arcnode-io/edp-module-assemblies/equipment/CMP-PDU-001/envelope.step

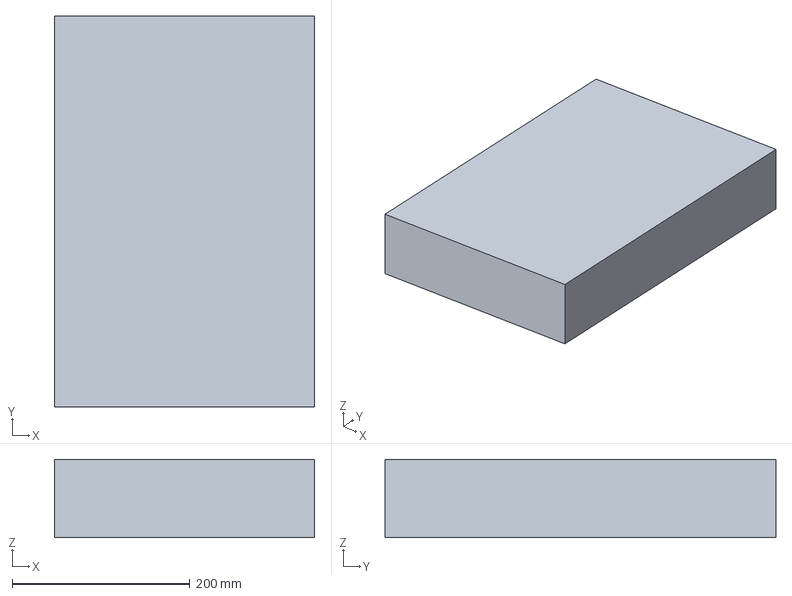
[picture p10: CAD file, 2026-10-03]
equipment/CMP-PDU-001/envelope.step
293.0 x 440.0 x 88.0 mm
