arcnode-io/edp-module-assemblies/equipment/CMP-RACK-001/envelope.step

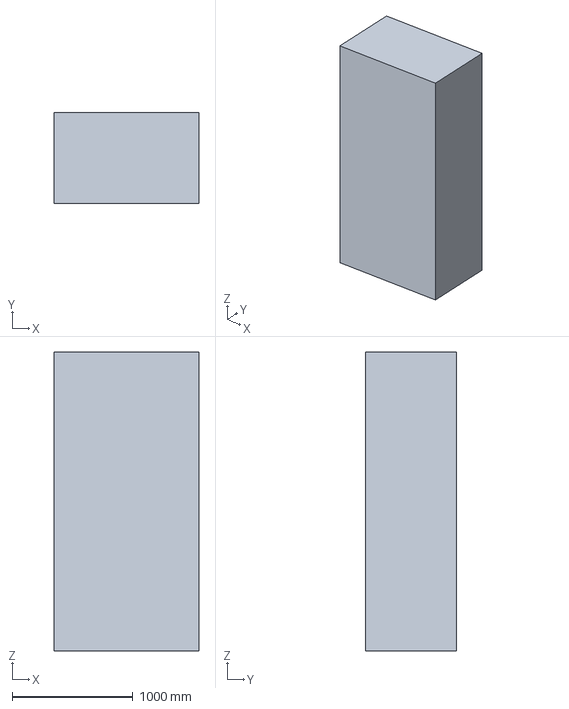
[picture p11: CAD file, 2026-05-09]
equipment/CMP-RACK-001/envelope.step
1200.0 x 750.0 x 2477.0 mm
