arcnode-io/edp-module-assemblies/equipment/CMP-SWITCH-001/envelope.step

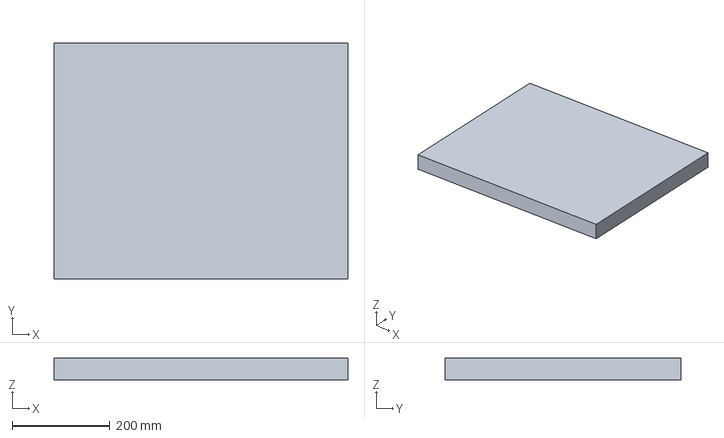
[picture p12: CAD file, 2026-05-09]
equipment/CMP-SWITCH-001/envelope.step
600.0 x 482.0 x 44.0 mm
