arcnode-io/edp-module-assemblies/equipment/CMP-SWITCH-002/envelope.step

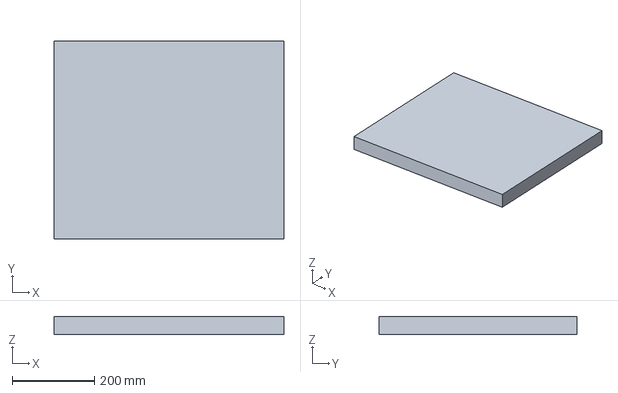
[picture p13: CAD file, 2026-05-09]
equipment/CMP-SWITCH-002/envelope.step
560.0 x 482.0 x 44.0 mm
