arcnode-io/edp-module-assemblies/equipment/EXT-BESS-001/envelope.step

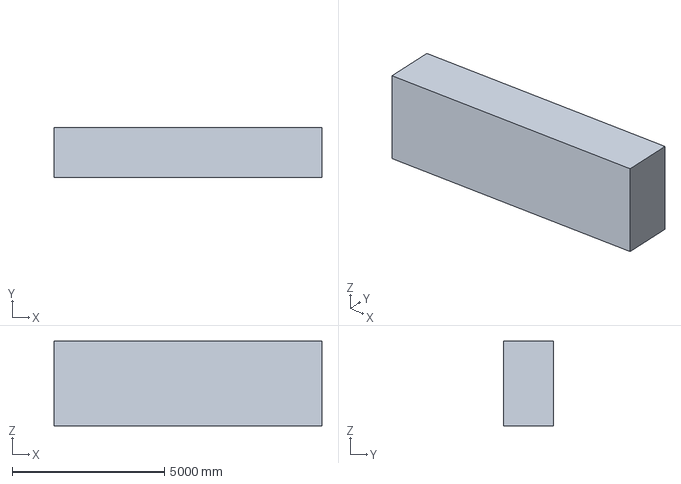
[picture p14: CAD file, 2026-05-09]
equipment/EXT-BESS-001/envelope.step
8800.0 x 1650.0 x 2785.0 mm
