arcnode-io/edp-module-assemblies/equipment/EXT-BESS-002/envelope.step

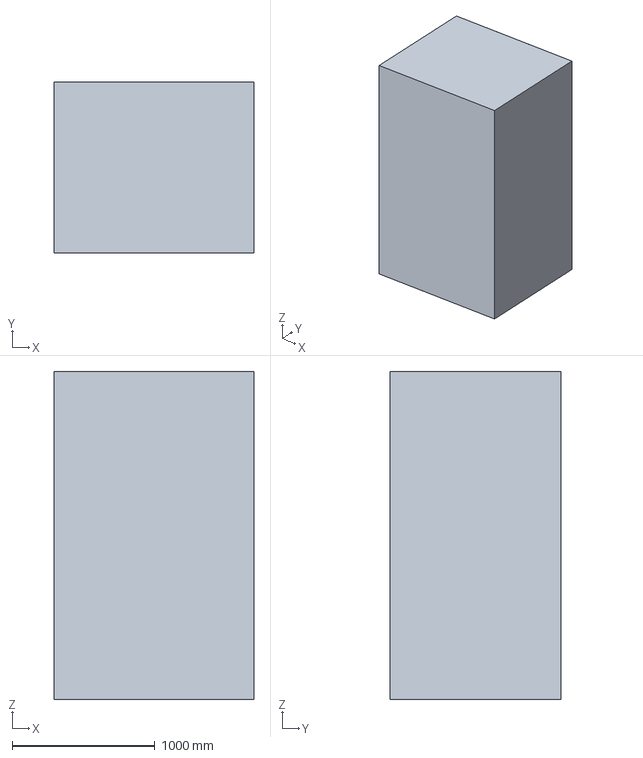
[picture p15: CAD file, 2026-05-09]
equipment/EXT-BESS-002/envelope.step
1400.0 x 1200.0 x 2300.0 mm
