arcnode-io/edp-module-assemblies/equipment/EXT-DC-001/envelope.step

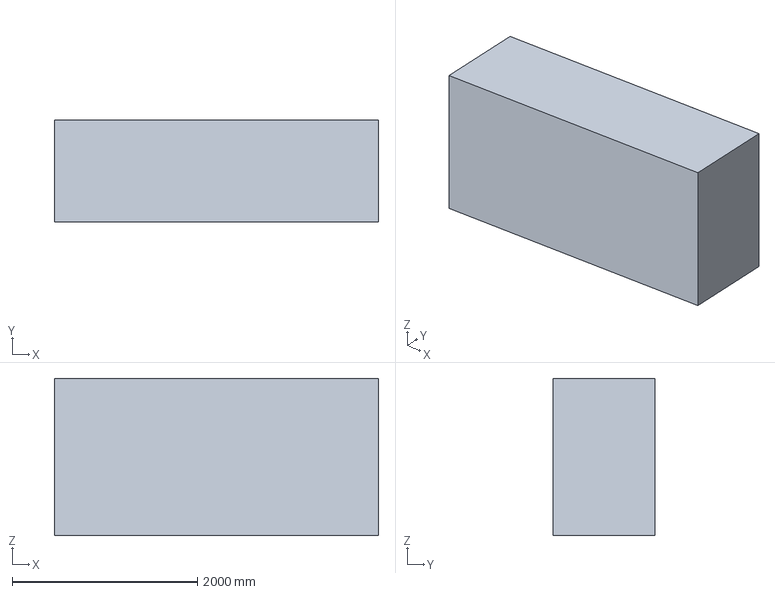
[picture p16: CAD file, 2026-05-09]
equipment/EXT-DC-001/envelope.step
3500.0 x 1100.0 x 1700.0 mm
