arcnode-io/edp-module-assemblies/equipment/EXT-DC-002/envelope.step

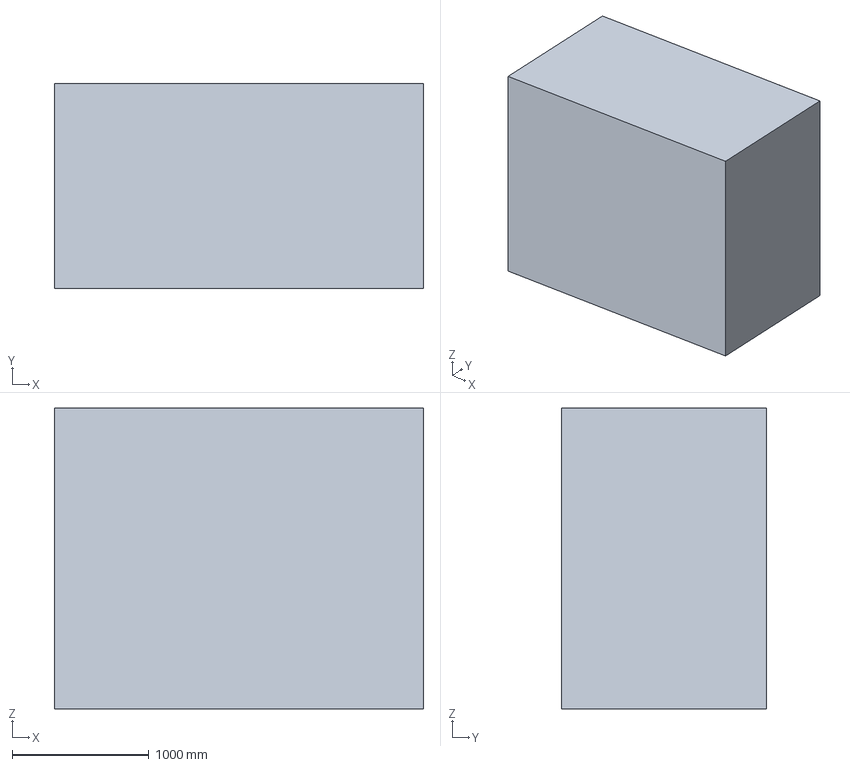
[picture p17: CAD file, 2026-05-09]
equipment/EXT-DC-002/envelope.step
2700.0 x 1500.0 x 2200.0 mm
