arcnode-io/edp-module-assemblies/equipment/GRD-MTR-001/envelope.step

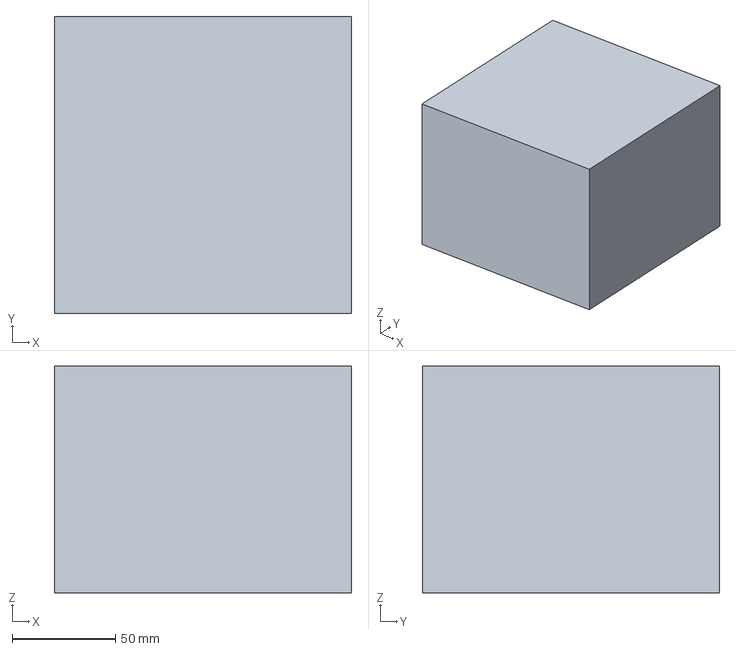
[picture p18: CAD file, 2026-05-09]
equipment/GRD-MTR-001/envelope.step
144.0 x 144.0 x 110.0 mm
