arcnode-io/edp-module-assemblies/equipment/GRD-PCS-001/envelope.step

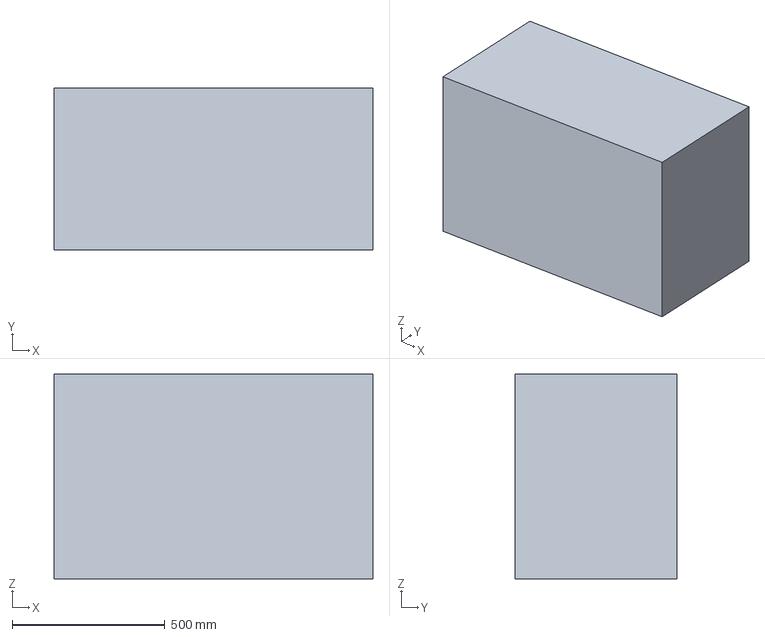
[picture p19: CAD file, 2026-05-09]
equipment/GRD-PCS-001/envelope.step
1045.0 x 530.0 x 670.0 mm
