arcnode-io/edp-module-assemblies/equipment/GRD-RLY-001/envelope.step

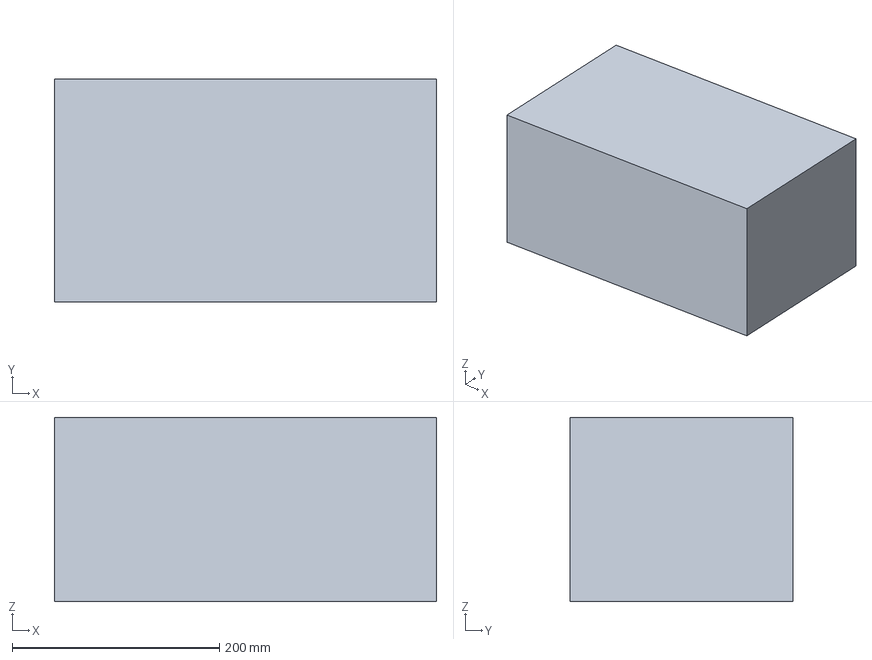
[picture p20: CAD file, 2026-05-09]
equipment/GRD-RLY-001/envelope.step
369.0 x 215.0 x 178.0 mm
