arcnode-io/edp-module-assemblies/equipment/GRD-SWG-001/envelope.step

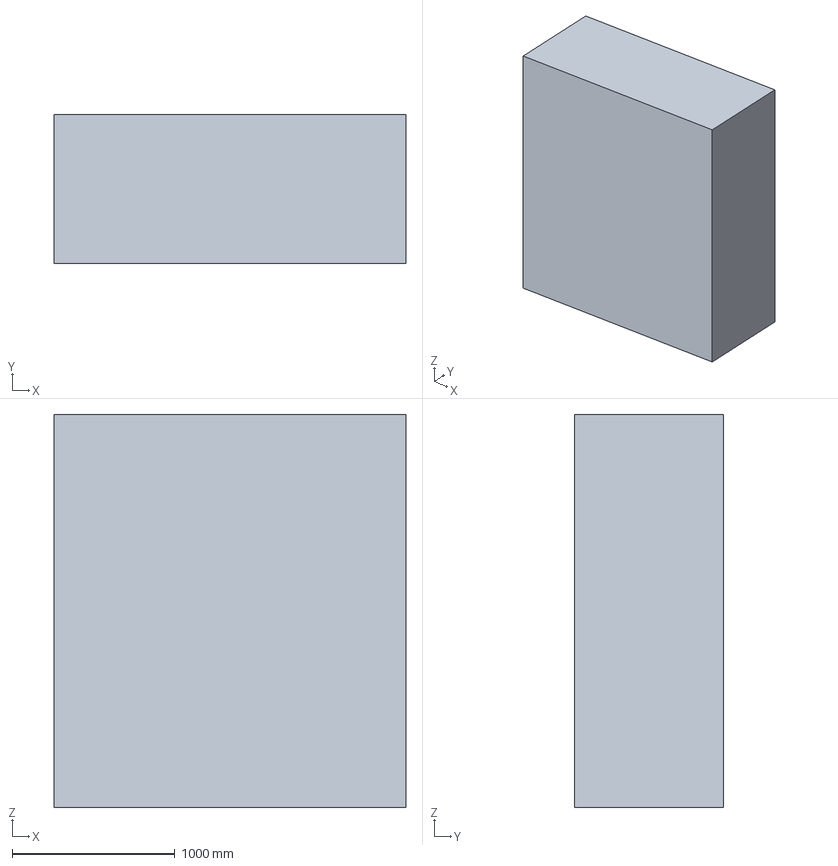
[picture p21: CAD file, 2026-05-09]
equipment/GRD-SWG-001/envelope.step
2159.0 x 914.0 x 2413.0 mm
