arcnode-io/edp-module-assemblies/equipment/GRD-XFM-001/envelope.step

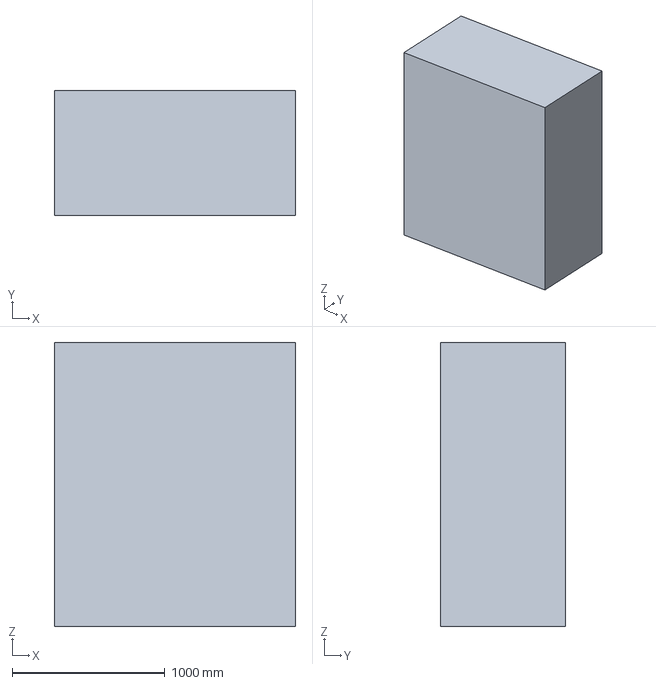
[picture p22: CAD file, 2026-05-09]
equipment/GRD-XFM-001/envelope.step
1580.0 x 820.0 x 1860.0 mm
