arcnode-io/edp-module-assemblies/equipment/CMP-PDU-001/spec.yaml

equipment_id: CMP-PDU-001
schema_version: "1"
category: pdu
vendor: Raritan (Legrand)
model_number: PX4-56A8I2R-C8E8F5V2 (2U horizontal, outlet metered + switched, 415V Wye 60A, 48A rated, 34.5kVA, 18 outlets)
description: 2U horizontal intelligent rack PDU, 415V 3ph Wye 60A (48A rated) 34.5kVA, inlet + branch + outlet metered (Class 0.5) and switched, 18 locking HDOT Cx outlets, Xerus platform
datasheet_url: https://cdn.raritan.com/product-selector/pdus/PX4-56A8I2R-C8E8F5V2/PX4-56A8I2R-C8E8F5V2-spec.pdf
datasheet_hash: TBD_compute_at_pipeline_run
step_source: null
fab_tier: dod_eligible
restricted_entities: null
install_video_url: null  # Track A enrichment — vendor-research pass populates
lead_time_weeks: 4
unit_cost_usd: null

spec:
  electrical:
    voltage_v: 415.0                  # 3-phase line-to-line
    voltage_range_v: [380.0, 440.0]
    current_a: 60.0
    phase: 3ph
    frequency_hz: 60.0
    power_kw: 34.5                    # 34.5 kVA: 415V × 48A rated (60A × 80% continuous) × √3
    power_factor_range: null
    efficiency_pct: null
    breaker_size_a: 60.0
    aic_rating_ka: null
    thd_pct: null
    fault_current_contribution_pu: null

  thermal:
    heat_load_kw: 0.05
    heat_rejection_kw: null
    coolant_compatibility: null
    flow_rate_lpm: null
    supply_temp_c: null
    return_temp_c: null
    pump_head_kpa: null
    internal_pressure_drop_kpa: null
    port_size_dn: null

  mechanical:
    weight_kg: 11.8                   # 26 lb
    dimensions_mm: [293, 440, 88]     # D × W × H
    container_type: 10ft_ISO_high_cube
    mounting: rack_19in
    mounting_notes: |
      2U horizontal in the rack U space (RACK-KIT-PX-2U). The rack's
      zero-U channels take only 4 PDUs, so the 6 needed for 2N go in U
      space. ARCNODE Compute Container uses 6× PDUs in 2N (3× A-side,
      3× B-side): ~13.3 kW each normally; on single-feed failure the
      surviving 3 carry the full ~80 kW at ~26.7 kW each, within the
      34.5 kVA rating. Enabled by 415V LV from GRD-XFM-001 secondary.
    rack_units: 2
    ip_rating: null
    lift_points: null
    ambient_temp_range_c: [-15, 60]
    max_elevation_m: null
    noise_dba_at_1m: null

  ports:
    - port_id: PWR_IN
      type: ac_power
      role: input
      connector_spec: IEC 60309 60A 3P+N+PE 6h pin and sleeve (240/415V Wye, 4P5W)
      mating_part: matching IEC 60309 60A 3P+N+PE 6h socket
      qty: 1
    - port_id: PWR_OUT_HDOT_CX
      type: ac_power
      role: output
      connector_spec: HDOT Cx hybrid C13/C19, locking, 16A (240V phase-to-neutral; 12× 16A branch breakers, 10 kAIC)
      mating_part: C14 or C20 plug
      qty: 18
    - port_id: NET_PRIMARY
      type: ethernet
      role: bidirectional
      connector_spec: RJ45 (Gigabit Ethernet)
      mating_part: null
      qty: 1
    - port_id: NET_SECONDARY
      type: ethernet
      role: bidirectional
      connector_spec: RJ45 (Gigabit Ethernet, redundant network)
      mating_part: null
      qty: 1
    - port_id: USB
      type: usb
      role: bidirectional
      connector_spec: USB-A
      mating_part: null
      qty: 1
    - port_id: SENSOR
      type: signal_digital
      role: input
      connector_spec: RJ45 (Legrand SmartSensor bus)
      mating_part: SmartSensor
      qty: 2

  control:
    protocol: snmp
    register_map_url: https://cdn1.raritan.com/download/pdu-g2/4.1.1/MIB_Usage_4.1.1_49961.pdf  # PDU2-MIB (all Xerus PDUs), inlet + inlet-pole sensor tables
    command_latency_ms: null
    step_response_ms: null
    control_modes:
      - autonomous_local
      - external_setpoint
      - per_outlet_switching
      - last_known_value_fallback
    black_start_capable: null

geometry:
  source: synthesized
  fidelity: bounding_box
  equipment_envelope_path: geometry/envelopes/CMP-PDU-001-equipment.step
  service_envelope_path: geometry/envelopes/CMP-PDU-001-service.step
  bounding_box:
    L_mm: 293.0
    W_mm: 440.0
    H_mm: 88.0
  service_clearance:
    front: 600.0
    rear: 0.0
    left: 50.0
    right: 50.0
    top: 100.0
    bottom: 100.0
    install_clearance: null

provenance:
  authored_by: skill:datasheet_extractor
  authored_date: 2026-04-28
  reviewed_by: TBD_pending_human_review
  reviewed_date: null
  confidence_flags:
    - field: spec.electrical.aic_rating_ka
      flag: missing
    - field: spec.thermal.heat_load_kw
      flag: assumed_default
      note: ~50W typical for intelligent PDU electronics.
    - field: control.command_latency_ms
      flag: missing
    - field: unit_cost_usd
      flag: missing
    - field: lead_time_weeks
      flag: low_confidence_extraction
      note: Server Technology typical 4 weeks for stocked SKUs; longer for custom configurations.

notes: |
  Raritan PX4 2U horizontal is the reference rack PDU for the ARCNODE
  Compute Container. The rack (CMP-RACK-001) has 4 zero-U PDU bays; 2N at
  80 kW on 34.5 kVA PDUs needs 6, so all 6 go in U space as one model.
  PRO3X was dropped (415V tops out at 17.3 kW); PRO4X C4G36RC matches
  electrically but is 0U-only.

  Sizing math for v1 HGX Compute Container (80 kW sustained):
  - 6× PX4 per Compute Container (3× A-side feed, 3× B-side feed)
  - Normal balanced operation: ~13.3 kW per PDU
  - Single-feed failure mode: surviving 3 PDUs carry full 80 kW = 26.7 kW
    each, within 34.5 kVA rating. TRUE 2N redundancy.
  - Headroom for B300/Blackwell Ultra upgrade (10% higher TDP per node):
    surviving-side load at ~88 kW = 29.3 kW per PDU, still within rating.

  HGX B200 power architecture (per CMP-NODE-001):
  - 4× PWS-6K61G-2R 6600W PSUs per node (2+2), each with two C20 inlets
    (16A each) that must both be live; phase-to-neutral 240V on 415Y/240V
  - Per-node sustained: ~10.5 kW; peak PSU capacity: 26.4 kW
  - PDU outlets per node: 8 (PSUs 1-2 → 4 cords on A, PSUs 3-4 → 4 on B);
    never split one PSU's two cords across feeds
  - 7 nodes × 8 = 56 node cords across 6 PDUs (108 Cx outlets), ~9-10 per PDU
  - Plus 2× C13 per ToR switch, 1× C13 per CDU, 1× C13 for ancillary
  - Outlet plan: at most one node cord per 16A branch breaker. A cord runs
    ~5.7A normally and ~11.5A with one feed lost, so two on one breaker
    (~23A) trip it on a feed loss. 12 breakers per PDU cover ~10 cords.
  - Inrush: <30A per PSU inlet (Supermicro), 8 inlets per node; stagger
    power-on across a PDU's breakers.

  HDOT Cx outlets accept either C14 or C20 plugs (16A, same as an IEC
  C19), so HGX node C20 plugs and switch/CDU C14 plugs share one SKU.

  EMS integration: SNMP via PDU2-MIB (Raritan MIB usage guide: applies to
  all Xerus devices, PX2/PX3/PX4 and PRO3X/PRO4X). Also Redfish, Modbus TCP
  and JSON-RPC per the PX4 spec sheet.

  Availability (2026-10-02): listed at PCNation, Tech-America, Connection
  ($3.1k-4.7k), all out of stock; quote Raritan direct.
  Per-outlet on/off control supported, useful for remote node power
  cycling without crash-cart access.

  Cybersecurity: Xerus platform supports HTTPS, SSH, SNMPv3, RADIUS,
  LDAPS, 802.1X, and signed firmware updates. NERC CIP eligible.

  Fab origin: Taiwan (GSA Advantage, GSIN 11000125269132, exact part).
  TAA compliant (Raritan TAA statement; Taiwan is a FAR 25.003 designated
  country); not BAA / Made in USA. Request a certificate of origin from
  Legrand where TAA is contractually load-bearing.

  ADR-005 (415V LV architecture): Trihal secondary set to 415Y/240V
  enables this PDU sizing.
