arcnode-io/edp-module-assemblies/equipment/EXT-BESS-001/spec.yaml

equipment_id: EXT-BESS-001
schema_version: "1"
category: bess
vendor: Tesla
model_number: Megapack 2 XL (PN 1848844-XX-Y)
description: 4 MWh AC-coupled BESS with integrated grid-forming bidirectional inverter
datasheet_url: http://www.cayugacounty.gov/DocumentCenter/View/33252/Tesla-Megapack-Datasheet
datasheet_hash: TBD_compute_at_pipeline_run
step_source: null
fab_tier: federal_civilian
restricted_entities:
  - DOD_1260H
install_video_url: null  # Track A enrichment — vendor-research pass populates
lead_time_weeks: null
unit_cost_usd: null

spec:
  electrical:
    voltage_v: 480.0
    voltage_range_v: null              # single nominal voltage
    current_a: 2887.0                  # computed: 2400 kVA / (480 × √3), 2-hour max
    phase: 3ph
    frequency_hz: 60.0                 # 50/60 Hz configurable
    power_kw: 1927.0                   # 2-hour rated AC power, C010/C011
    power_factor_range: null
    efficiency_pct: 91.7               # round-trip system efficiency, 2-hour C010/C011
    breaker_size_a: null
    aic_rating_ka: null
    thd_pct: null
    fault_current_contribution_pu: null

  thermal: null                         # external BESS handles its own thermal

  mechanical:
    weight_kg: 38100.0
    dimensions_mm: [8800, 1650, 2785]  # L × W × H (W 8800 × D 1650 × H 2785 per datasheet)
    container_type: null
    mounting: pad
    mounting_notes: |
      Pad-mounted with seismic anchoring per local code. Customer-owned pad
      civil works. Service clearance and access are customer site planning,
      not ARCNODE Grid Container integration.
    rack_units: null
    ip_rating: IP66                    # main enclosure; thermal system is IP20
    lift_points: null
    ambient_temp_range_c: [-30, 50]
    max_elevation_m: null
    noise_dba_at_1m: null

  ports:
    - port_id: AC1
      type: ac_power
      role: bidirectional              # 480V 3-phase to ARCNODE Grid Container AC bus
      connector_spec: TBD
      mating_part: null
      qty: 1
    - port_id: COMMS
      type: ethernet
      role: bidirectional              # Modbus TCP / DNP3
      connector_spec: RJ45 (assumed)
      mating_part: null
      qty: 1

  control:
    protocol: modbus_tcp                # primary; DNP3 also supported
    register_map_url: null
    command_latency_ms: null
    step_response_ms: null
    control_modes:
      - grid_forming                   # confirmed via C&I Off-Grid Microgrid archetype
      - grid_following                 # standard utility-tied operation
      - direct_real_power
      - direct_reactive_power
      - frequency_support
      - virtual_inertia
      - ramp_rate_control
      - voltage_control
      - power_factor_control
    black_start_capable: true          # supported via C&I Off-Grid Microgrid archetype

geometry:
  source: synthesized
  fidelity: bounding_box
  equipment_envelope_path: geometry/envelopes/EXT-BESS-001-equipment.step
  service_envelope_path: geometry/envelopes/EXT-BESS-001-service.step
  bounding_box:
    L_mm: 8800.0
    W_mm: 1650.0
    H_mm: 2785.0
  service_clearance:
    front: 1500.0                      # service access, AC and comms connections
    rear: 1000.0                       # deflagration vent clearance per safety datasheet
    left: 1000.0
    right: 1000.0
    top: 3000.0                        # deflagration vents on roof; required clearance
    bottom: 0.0                        # pad-mounted
    install_clearance:
      direction: top
      value_mm: 4000.0                 # crane lift clearance (38 t unit)

provenance:
  authored_by: skill:datasheet_extractor
  authored_date: 2026-04-28
  reviewed_by: TBD_pending_human_review
  reviewed_date: null
  confidence_flags:
    - field: fab_tier
      flag: ambiguous
      note: |
        Tesla assembles Megapack in Lathrop CA (US) and Shanghai (China-fab,
        post-2024). Cells sourced from CATL (China) or LG Energy Solution
        (Korea/US). Set to federal_civilian as the conservative tier given
        cell-sourcing uncertainty. DOD-eligible deployments require cell-
        source verification at procurement time.
    - field: restricted_entities
      flag: assumed_default
      note: |
        DOD_1260H flagged because CATL cells are common in Megapack
        production. If deployment specifies LG-sourced cells with US fab,
        this flag may be removed per-unit. Verify with Tesla at procurement.
    - field: spec.electrical.power_factor_range
      flag: missing
      note: Datasheet does not state PF range. Modern utility BESS typically [-1.0, 1.0] but not vendor-confirmed.
    - field: spec.electrical.fault_current_contribution_pu
      flag: missing
      note: Required per §6.1 grid-forming guidance for fault studies. Not in public datasheet. Sales touch follow-up.
    - field: spec.electrical.thd_pct
      flag: missing
    - field: spec.electrical.aic_rating_ka
      flag: missing
    - field: spec.electrical.breaker_size_a
      flag: missing
    - field: spec.mechanical.lift_points
      flag: missing
      note: 38 t unit; lift point count not stated. Material for crane planning.
    - field: spec.mechanical.noise_dba_at_1m
      flag: missing
    - field: spec.mechanical.max_elevation_m
      flag: missing
    - field: spec.ports.AC1.connector_spec
      flag: missing
      note: AC connection style (lugs, busbar, conduit) not in public datasheet.
    - field: control.register_map_url
      flag: missing
      note: Modbus TCP and DNP3 register maps gated. Sales touch required for EMS integration.
    - field: control.command_latency_ms
      flag: missing
    - field: control.step_response_ms
      flag: missing
    - field: unit_cost_usd
      flag: missing
    - field: lead_time_weeks
      flag: missing

notes: |
  Tesla Megapack 2 XL is the AC-coupled BESS profile primary entry per
  ADR-001 (Bring Your Own BESS). Customer-supplied equipment; ARCNODE does
  not procure, ship, or install. ARCNODE's Grid Container interfaces with the
  Megapack over a single AC connection (480V 3-phase) and a single Ethernet
  comms link.

  Configuration options at deployment:
  - 2-Hour C010/C011: 1927 kW / 3854 kWh per Megapack
  - 4-Hour C010/C011: 979 kW / 3916 kWh per Megapack
  - 4-Hour C012: 1075 kW / 4300 kWh per Megapack
  - Non-standard 8-Hour available via Tesla configuration
  Sizing engine selects configuration based on customer autonomy requirement.

  Grid-forming capability confirmed via two sources: (1) the datasheet
  Archetypes list explicitly includes "C&I Off-Grid Microgrid", which
  requires grid-forming inverter behavior; (2) Tesla Energy Q1 2026
  reporting confirms grid-forming inverters with black-start capability
  in the current generation. Resolves Open Item 1 from ADR-001.

  Cell sourcing: Tesla uses CATL (China) and LG Energy Solution (Korea/US)
  cells across the Megapack production fleet. Cell origin varies per unit
  and per production run. For DOD-eligible deployments, cell-source
  certification must be obtained from Tesla at procurement; default
  classification is federal_civilian with DOD_1260H flag as conservative
  default.

  Protocol stack: Modbus TCP and DNP3 are standard. REST API was offered
  in earlier Megapack revisions but is not listed in the November 2025
  REV 2.0 datasheet — Tesla appears to have simplified the supported
  protocol stack. EMS integration uses Modbus TCP per ARCNODE convention.

  Safety: deflagration vents on the roof are the gating clearance
  consideration. Service envelope captures 3000 mm top clearance for
  vent operation; install_clearance separately captures crane lift
  clearance for the 38 t unit. Both required.

  Warranty: 15 years standard, extendable to 20 with Capacity Maintenance
  Agreement (CMA). Tesla requires a maintenance service agreement; capture
  in BOM generator dependency rules as a recurring-cost line item.

  Megablock (announced for late 2026): Tesla's planned Megablock product
  is 4× Megapack v3 + transformer + switchgear. Overlaps with ARCNODE's
  Grid Container function in the AC-coupled profile. Re-evaluate ARCNODE
  positioning when Megablock specs are published. Tracked as Open Item 4
  in ADR-001.
